Rukenshia/terminal.scale/docs/schematics.kicad_sch

## KiCad design docs/schematics.kicad_sch (2025-04-18)

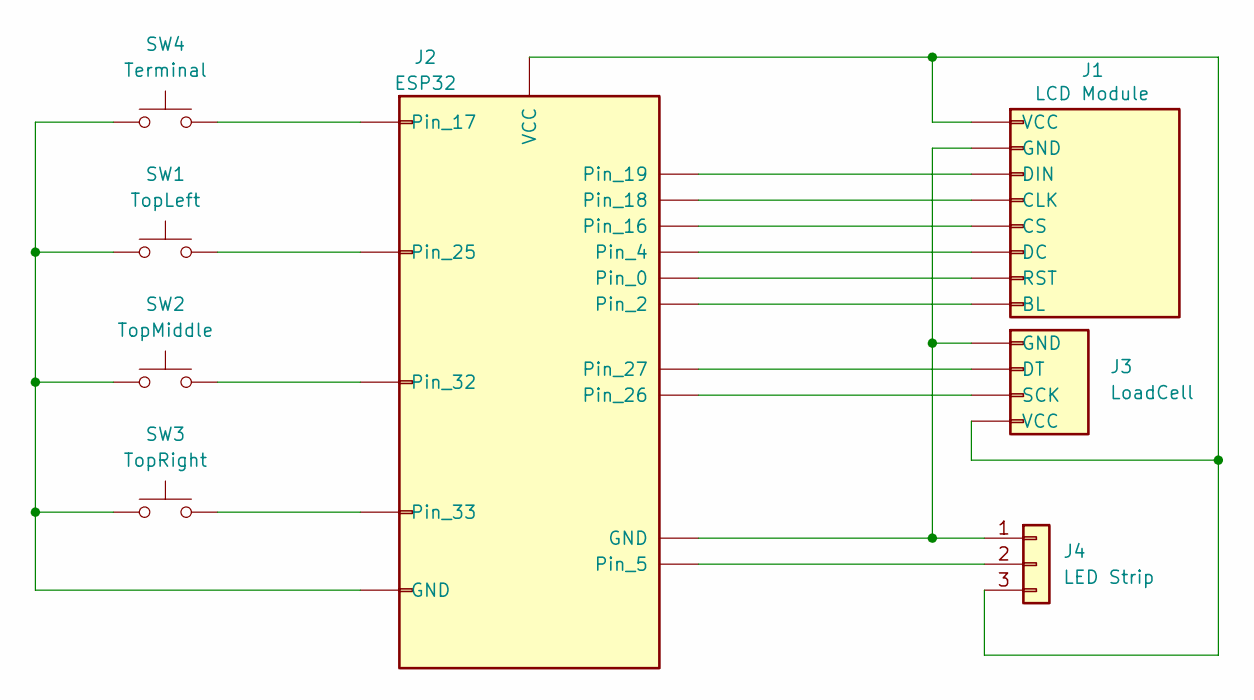
[picture p18: schematic schematics.kicad_sch]

Parts:
J1: LCD Module
J2: ESP32
J3: LoadCell
J4: LED Strip
SW1: TopLeft
SW2: TopMiddle
SW3: TopRight
SW4: Terminal

Connections:
unnamed: J1.1 (VCC), J2.2 (VCC), J3.4 (VCC), J4.3
unnamed: J1.2 (GND), J2.GND, J3.1 (GND), J4.1
unnamed: J1.3 (DIN), J2.19
unnamed: J1.4 (CLK), J2.18
unnamed: J1.5 (CS), J2.16
unnamed: J1.6 (DC), J2.4
unnamed: J1.7 (RST), J2.0
unnamed: J1.8 (BL), J2.2 (VCC)
unnamed: J2.5, J4.2
unnamed: J2.17, SW4.2
unnamed: J2.25, SW1.2
unnamed: J2.26, J3.3 (SCK)
unnamed: J2.27, J3.2 (DT)
unnamed: J2.32, SW2.2
unnamed: J2.33, SW3.2
unnamed: J2.GND, SW1.1, SW2.1, SW3.1, SW4.1
