Rukenshia/terminal.scale/src/store.cpp

#include "store.h"
#include "debug.h"
#include "buttons.h"

void Store::exit()
{
    reset();
    ledStrip.turnOff();
}

void Store::draw()
{
    if (!tainted)
    {
        return;
    }
    tainted = false;

    if (ui.menu->current == STORE_ORDERS)
    {
        drawOrders();
        return;
    }
    else if (ui.menu->current == STORE_BROWSE)
    {
        drawProducts();
        return;
    }

    // clear the screen except menu clearance
    tft.fillRect(0, Menu::menuClearance, tft.width(), tft.height() - Menu::menuClearance, BACKGROUND_COLOR);

    auto bounds = ui.typeText("Store", titleText);
    delay(1000);
    ui.wipeText(bounds);

    tft.setFreeFont(&GeistMono_VariableFont_wght18pt7b);
    tft.setTextColor(ACCENT_COLOR);
}

void Store::loadOrders()
{
    if (ordersLoaded)
    {
        Serial.println("Orders already loaded");
        return;
    }

    tft.fillScreen(BACKGROUND_COLOR);
    auto bounds = ui.typeTitle("Loading orders");
    ui.startBlinking();

#ifdef NO_WIFI
    orders = {
        {"id1", "2025-01-01T12:34:56Z", 1, {"John Doe", "123 Main St", "", "New York", "NY", "10001", "USA", "555-1234"}, {1000, 50}, {"UPS", "1234567890", "SHIPPED", "http://example.com/track"}},
        {"id2", "2024-12-20T34:56:00Z", 2, {"Jane Smith", "456 Elm St", "", "Los Angeles", "CA", "90001", "USA", "555-5678"}, {2000, 100}, {"FedEx", "0987654321", "DELIVERED", "http://example.com/track"}},
    };
#else
    orders = terminalApi.getOrders();
    Serial.printf("Loaded %d orders\n", orders.size());
#endif
    ordersLoaded = true;

    ui.stopBlinking();
    ui.wipeText(bounds);

    if (orders.empty())
    {
        ui.typeTitle("No orders found");
        delay(2000);

        ui.menu->selectMenu(STORE);
        return;
    }

    recalcMenuButtons(orderIndex, orders.size());
    ui.menu->taint();
}

void Store::drawOrders()
{
    if (!ordersLoaded)
    {
        loadOrders();

        if (orders.empty())
        {
            return;
        }
        recalcMenuButtons(orderIndex, orders.size());
    }

    tft.fillRect(0, Menu::menuClearance - tft.fontHeight(), tft.width(), tft.height(), BACKGROUND_COLOR);

    const uint16_t startY = Menu::menuClearance + 40;

    tft.setTextColor(ACCENT_COLOR);
    tft.setCursor(20, startY);

    auto &order = orders[orderIndex];
    String orderId = order.id.substring(0, 16) + "..";
    ui.setIdealFont(orderId.c_str(), 30);

    tft.print(orderId);

    String status = "UNKNOWN";
    if (!order.tracking.status.isEmpty())
    {
        status = order.tracking.status;
    }

    tft.setCursor(20, startY + 40);

    String subheaderText = order.created.substring(0, 10) + " - " + status;
    ui.setIdealFont(subheaderText.c_str(), 30);
    tft.setTextColor(TEXT_COLOR);
    tft.print(order.created.substring(0, 10).c_str());
    tft.print(" - ");

    if (status == "DELIVERED")
    {
        tft.setTextColor(0x05C8);
    }
    else if (status == "UNKNOWN")
    {
        tft.setTextColor(0xD9A7);
    }
    else
    {
        tft.setTextColor(0x44FC);
    }

    tft.print(status.c_str());

    ui.drawProgressIndicator(orderIndex, orders.size());
}

void Store::recalcMenuButtons(int index, int size)
{
    bool shouldRedraw = false;

    if (index == size - 1)
    {
        ui.menu->hideButton(MenuButton::RIGHT);
        shouldRedraw = true;
    }
    else if (!ui.menu->isButtonVisible(MenuButton::RIGHT))
    {
        ui.menu->showButton(MenuButton::RIGHT);
        shouldRedraw = true;
    }

    if (index == 0)
    {
        ui.menu->hideButton(MenuButton::LEFT);
        shouldRedraw = true;
    }
    else if (!ui.menu->isButtonVisible(MenuButton::LEFT))
    {
        ui.menu->showButton(MenuButton::LEFT);
        shouldRedraw = true;
    }

    if (shouldRedraw)
    {
        ui.menu->redraw();
    }

    ledStrip.scrollIndicator(index, size);
}

void Store::nextOrder()
{
    orderIndex++;
    if (orderIndex >= orders.size())
    {
        orderIndex--;
        return;
    }

    recalcMenuButtons(orderIndex, orders.size());
    taint();
}

void Store::previousOrder()
{
    if (orderIndex == 0)
    {
        return;
    }

    orderIndex--;
    recalcMenuButtons(orderIndex, orders.size());
    taint();
}

void Store::drawProducts()
{
    if (!productsLoaded)
    {
        loadProducts();

        if (products.empty())
        {
            return;
        }
        recalcMenuButtons(productIndex, products.size());
    }

    uint16_t y = 60 + 60;
    tft.fillRect(0, Menu::menuClearance - tft.fontHeight(), tft.width(), tft.height(), BACKGROUND_COLOR);

    tft.setFreeFont(&GeistMono_VariableFont_wght14pt7b);
    tft.setTextColor(ACCENT_COLOR);
    tft.setCursor(tft.width() - 20 - tft.textWidth("B") / 2, y);
    tft.print("B");
    tft.setCursor(tft.width() - 20 - tft.textWidth("U") / 2, y + tft.fontHeight() + 4);
    tft.print("U");
    tft.setCursor(tft.width() - 20 - tft.textWidth("Y") / 2, y + tft.fontHeight() * 2 + 8);
    tft.print("Y");

    y += 20;

    tft.setFreeFont(&GeistMono_VariableFont_wght18pt7b);

    tft.setTextColor(ACCENT_COLOR);
    tft.setCursor(20, y);

    auto &product = products[productIndex];
    ui.setIdealFont(product.name.c_str());
    tft.print(product.name.c_str());

    y += 40;
    tft.setCursor(20, y);

    String subheader = product.variants[0].name + " - $" + String(product.variants[0].price / 100.0f, 2);
    ui.setIdealFont(subheader.c_str(), nonTitleFonts);
    tft.setTextColor(TEXT_COLOR);
    tft.print(subheader.c_str());

    ui.drawProgressIndicator(productIndex, products.size());
}

void Store::loadProducts()
{
    tft.fillScreen(BACKGROUND_COLOR);
    auto bounds = ui.typeTitle("Loading products");
    ui.startBlinking();

#ifdef NO_WIFI
    products = std::vector<Product>{
        Product{"id1", "flow", "coffee", {Variant{"id1", "12oz", 1000}}},
        Product{"id2", "[object Object]", "covfefe", {Variant{"id2", "24oz", 2000}}},
    };
#else
    products = terminalApi.getProducts();
#endif

    // FIXME: would be nice to support more than 12oz bags
    // @terminal.shop when in europe?
    for (auto &product : products)
    {
        product.variants.erase(
            std::remove_if(product.variants.begin(), product.variants.end(),
                           [](const Variant &variant)
                           { return variant.name != "12oz"; }),
            product.variants.end());
    }

    productsLoaded = true;

    ui.stopBlinking();
    ui.wipeText(bounds);

    if (products.empty())
    {
        ui.typeTitle("No products found");
        delay(2000);

        ui.menu->selectMenu(STORE);
        return;
    }

    ui.menu->taint();
}

void Store::previousProduct()
{
    if (productIndex == 0)
    {
        return;
    }

    productIndex--;

    recalcMenuButtons(productIndex, products.size());
    taint();
}

void Store::nextProduct()
{
    if (productIndex >= products.size() - 1)
    {
        return;
    }

    productIndex++;

    recalcMenuButtons(productIndex, products.size());
    taint();
}

void Store::buyProduct()
{
    tft.setFreeFont(&GeistMono_VariableFont_wght18pt7b);
    tft.fillScreen(BACKGROUND_COLOR);
    tft.setTextColor(TEXT_COLOR);

    auto tw = tft.textWidth("Hold to buy");
    tft.setCursor(tft.width() / 2 - tw / 2, tft.height() / 2);
    tft.print("Hold to buy");

    const uint16_t initialCircleSize = 20;
    const uint16_t animationDuration = 3000; // 3 seconds total
    const uint16_t maxCircleSize = tft.width() * 2 + initialCircleSize / 2;
    const uint16_t circleX = tft.width() + initialCircleSize / 2;
    const uint16_t circleY = tft.height() / 2 + 40;

    tft.fillCircle(circleX, circleY, initialCircleSize, ACCENT_COLOR);
    delay(1000);

    bool finished = false;
    unsigned long startTime = millis();
    unsigned long elapsedTime = 0;

    uint16_t circleSize = initialCircleSize;

    while (digitalRead(PIN_TERMINAL_BUTTON) == LOW)
    {
        elapsedTime = millis() - startTime;

        float linearProgress = min(1.0f, (float)elapsedTime / animationDuration);
        // Easing function: accelerate towards the end (ease-in-quad)
        float easedProgress = linearProgress * linearProgress;
        circleSize = (easedProgress * maxCircleSize) + initialCircleSize;

        tft.fillCircle(circleX, circleY, circleSize, ACCENT_COLOR);

        auto color = RgbColor::LinearBlend(
            RgbColor(194, 126, 0),
            RgbColor(255, 94, 0), linearProgress);
        ledStrip.reverseProgress(linearProgress, color);

        if (elapsedTime >= animationDuration)
        {
            finished = true;
            break;
        }
        delay(10);
    }

    if (!finished)
    {
        ui.menu->taint();
        taint();
        recalcMenuButtons(productIndex, products.size());
        return;
    }

    orderProduct(products[productIndex],
                 products[productIndex].variants[0]);
}

void Store::orderProduct(String bagName)
{
    if (!productsLoaded)
    {
        loadProducts();
        if (products.empty())
        {
            return;
        }
    }

    auto index = std::find_if(products.begin(), products.end(),
                              [&bagName](const Product &product)
                              {
                                  return product.name == bagName;
                              }) -
                 products.begin();

    orderProduct(products[index], products[index].variants[0]);
}

void Store::orderProduct(Product product, Variant variant)
{
    tft.fillScreen(BACKGROUND_COLOR);
    auto bounds = ui.typeTitle("Clearing cart...");
    if (terminalApi.clearCart())
    {
        Serial.println("Cart cleared");
    }
    else
    {
        Serial.println("Failed to clear cart");
    }

    ui.wipeText(bounds);
    bounds = ui.typeTitle("Adding to cart...");
    Cart *cart = terminalApi.addItemToCart(products[productIndex].variants[0].id.c_str(), 1);
    if (!cart)
    {
        taint();
        ui.menu->taint();
        return;
    }
    ui.wipeText(bounds);

    bounds = ui.typeTitle(String("Subtotal: $" + String((float)cart->subtotal / 100, 2)).c_str());
    delay(3000);
    ui.wipeText(bounds);

    bounds = ui.typeTitle("Placing order...");
    Order *order = terminalApi.convertCartToOrder();
    if (!order)
    {
        taint();
        ui.menu->taint();
        return;
    }

    ui.wipeText(bounds);
    ui.typeTitle("Order placed");
    ledStrip.purchaseAnimation();
    delay(5000);
    ui.wipeText(bounds);

    ledStrip.turnOff();
    taint();
    ui.menu->selectMenu(MAIN_MENU);
}

void Store::openToReorder(String bagName)
{
    tft.fillScreen(BACKGROUND_COLOR);

    loadProducts();
    if (products.empty())
    {
        Serial.println("No products found");
        return;
    }

    ui.menu->selectMenu(STORE_BROWSE);

    // set index
    productIndex = std::find_if(products.begin(), products.end(),
                                [&bagName](const Product &product)
                                {
                                    return product.name == bagName;
                                }) -
                   products.begin();
    Serial.printf("Product index: %d\n", productIndex);
    if (productIndex >= products.size())
    {
        productIndex = 0;
    }

    Serial.printf("Product name: %s\n", products[productIndex].name.c_str());
    recalcMenuButtons(productIndex, products.size());
    taint();
}
