Rukenshia/terminal.scale/include/HelvetiPixelFont_wght12.h

const uint8_t HelvetiPixel12pt7bBitmaps[] PROGMEM = {
  0x00, 0xFF, 0xFF, 0xCF, 0xDE, 0xF7, 0xBD, 0x80, 0x1B, 0x0D, 0x86, 0xDF,
  0xFF, 0xFB, 0x61, 0xB1, 0xFF, 0xFF, 0xB6, 0x1B, 0x0D, 0x80, 0x18, 0x18,
  0x7C, 0xFF, 0xDB, 0xD8, 0xFC, 0x7C, 0x1B, 0xDB, 0xDB, 0x7C, 0x7C, 0x18,
  0x30, 0xC7, 0xC6, 0x36, 0x31, 0xB6, 0x0F, 0xB0, 0x19, 0x80, 0x19, 0x80,
  0xDF, 0x06, 0xD8, 0xC6, 0xC6, 0x3E, 0x30, 0xC0, 0x1C, 0x0F, 0xE1, 0x8C,
  0x31, 0x87, 0xF0, 0x38, 0x1B, 0x1F, 0x7F, 0xC3, 0x98, 0x73, 0xFF, 0xBE,
  0x30, 0xFF, 0xC0, 0x1B, 0xD8, 0xCE, 0x63, 0x18, 0xC6, 0x38, 0xC6, 0x3C,
  0x60, 0xC7, 0x18, 0xC7, 0x8C, 0x63, 0x18, 0xDE, 0xC6, 0x73, 0x00, 0xDB,
  0xDB, 0x7C, 0xFF, 0xDB, 0x18, 0x18, 0x18, 0xFF, 0xFF, 0x18, 0x18, 0x18,
  0x6D, 0xFC, 0xFF, 0xC0, 0xF0, 0x18, 0xC6, 0x37, 0xB1, 0x8C, 0x66, 0x31,
  0x8C, 0x60, 0x7C, 0xFF, 0xC3, 0xC3, 0xC3, 0xC3, 0xC3, 0xC3, 0xC3, 0xC3,
  0xFF, 0x7C, 0x19, 0xCF, 0xBD, 0x8C, 0x63, 0x18, 0xC6, 0x30, 0x7C, 0xFF,
  0xC3, 0x03, 0x0F, 0x0C, 0x18, 0x78, 0x60, 0xC0, 0xFF, 0xFF, 0x7C, 0xFF,
  0xC3, 0x03, 0x1F, 0x1C, 0x03, 0x03, 0x03, 0xC3, 0xFF, 0x7C, 0x03, 0x07,
  0x83, 0xC3, 0x67, 0xB3, 0x1B, 0x0D, 0xFF, 0xFF, 0x81, 0x80, 0xC0, 0x60,
  0xFF, 0xFF, 0xC0, 0xC0, 0xFC, 0xFC, 0x03, 0x03, 0x03, 0xC3, 0xFF, 0x7C,
  0x7C, 0xFF, 0xC3, 0xC0, 0xFC, 0xFC, 0xC3, 0xC3, 0xC3, 0xC3, 0xFF, 0x7C,
  0xFF, 0xFF, 0x03, 0x0C, 0x0C, 0x0C, 0x18, 0x18, 0x18, 0x60, 0x60, 0x60,
  0x7C, 0xFF, 0xC3, 0xC3, 0xFF, 0x7C, 0xC3, 0xC3, 0xC3, 0xC3, 0xFF, 0x7C,
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
  {   377,   8,  12,  11,    1,  -11 },   // 0x46 'F'
  {   389,  11,  12,  12,    0,  -11 },   // 0x47 'G'
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

const GFXfont HelvetiPixel12pt7b PROGMEM = {
  (uint8_t  *)HelvetiPixel12pt7bBitmaps,
  (GFXglyph *)HelvetiPixel12pt7bGlyphs,
  0x20, 0x7E, 22 };

// Approx. 1628 bytes
