Rukenshia/terminal.scale/include/GeistMonoVariableFont_wght10.h

const uint8_t GeistMono_VariableFont_wght10pt7bBitmaps[] PROGMEM = {
  0x00, 0xFF, 0xFF, 0xE0, 0xF0, 0xCE, 0x72, 0x94, 0xA5, 0x20, 0x19, 0x86,
  0x61, 0x90, 0x44, 0x7F, 0xC4, 0xC3, 0x30, 0xC8, 0x22, 0x3F, 0xE2, 0x61,
  0x98, 0x64, 0x11, 0x00, 0x0C, 0x03, 0x01, 0xE1, 0xFC, 0xCD, 0xB3, 0x2C,
  0xCD, 0xB0, 0x7C, 0x07, 0xC0, 0xD9, 0x33, 0xCC, 0xF3, 0x37, 0xD8, 0xFC,
  0x0C, 0x03, 0x00, 0x78, 0x64, 0x8C, 0xCC, 0x8C, 0xD8, 0xCD, 0x04, 0xB0,
  0x36, 0x00, 0x4C, 0x0F, 0xE0, 0xA2, 0x1A, 0x33, 0x22, 0x23, 0x26, 0x1C,
  0x1E, 0x07, 0x60, 0xC4, 0x18, 0x83, 0x30, 0x3C, 0x07, 0x01, 0xE0, 0x66,
  0x68, 0x6F, 0x0D, 0xE0, 0xE6, 0x1C, 0x7E, 0xC0, 0xFF, 0xF8, 0x32, 0x64,
  0xCC, 0xCC, 0x8C, 0xCC, 0xC4, 0x62, 0x30, 0x8C, 0x66, 0x23, 0x33, 0x33,
  0x33, 0x26, 0x64, 0xC0, 0x49, 0xE3, 0x3F, 0x71, 0x24, 0x80, 0x0C, 0x03,
  0x00, 0xC3, 0xFF, 0xFF, 0xC3, 0x00, 0xC0, 0x30, 0x0C, 0x00, 0xF6, 0x80,
  0xFC, 0xF0, 0x03, 0x02, 0x06, 0x06, 0x04, 0x0C, 0x08, 0x08, 0x18, 0x10,
  0x30, 0x30, 0x20, 0x60, 0x60, 0x40, 0xC0, 0x3E, 0x1D, 0xC6, 0x1B, 0x0E,
  0xC6, 0xF1, 0xBC, 0xCF, 0x23, 0xD8, 0xF4, 0x3F, 0x19, 0x86, 0x73, 0x0F,
  0x80, 0x04, 0x01, 0x07, 0xC1, 0xF0, 0x04, 0x01, 0x00, 0x40, 0x10, 0x04,
  0x01, 0x00, 0x40, 0x10, 0xFF, 0xFF, 0xF0, 0x3F, 0x1C, 0xE6, 0x0F, 0x03,
  0x00, 0xC0, 0x60, 0x38, 0x3C, 0x1C, 0x0C, 0x06, 0x03, 0x00, 0xFF, 0xFF,
  0xF0, 0x3F, 0x1C, 0xEC, 0x18, 0x02, 0x01, 0x80, 0xE0, 0xE0, 0x0E, 0x00,
  0x80, 0x3C, 0x0F, 0x03, 0x63, 0x8F, 0xC0, 0x03, 0x01, 0xC0, 0x70, 0x34,
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
  {   504,  10,  14,  12,    1,  -13 },   // 0x47 'G'
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

const GFXfont GeistMono_VariableFont_wght10pt7b PROGMEM = {
  (uint8_t  *)GeistMono_VariableFont_wght10pt7bBitmaps,
  (GFXglyph *)GeistMono_VariableFont_wght10pt7bGlyphs,
  0x20, 0x7E, 25 };

// Approx. 1972 bytes
