Rukenshia/terminal.scale/include/GeistMonoVariableFont_wght14.h

const uint8_t GeistMono_VariableFont_wght14pt7bBitmaps[] PROGMEM = {
  0x00, 0xDB, 0x6D, 0xB6, 0xDB, 0x6C, 0x00, 0xFF, 0x80, 0xCF, 0x9F, 0x3E,
  0x7C, 0xF9, 0xB3, 0x66, 0xCC, 0x06, 0x18, 0x18, 0xC0, 0x63, 0x01, 0x8C,
  0x0C, 0x30, 0xFF, 0xF7, 0xFF, 0xC3, 0x18, 0x0C, 0x60, 0x71, 0x81, 0x86,
  0x06, 0x18, 0x7F, 0xFB, 0xFF, 0xE1, 0x8C, 0x0C, 0x30, 0x30, 0xC0, 0xC6,
  0x03, 0x18, 0x00, 0x03, 0x00, 0x0C, 0x00, 0x30, 0x07, 0xF8, 0x3F, 0xF1,
  0xCC, 0xE6, 0x31, 0x98, 0xC7, 0x63, 0x1D, 0xCC, 0x07, 0xB0, 0x0F, 0xC0,
  0x0F, 0xE0, 0x0F, 0xE0, 0x33, 0xC0, 0xC7, 0xE3, 0x0D, 0x8C, 0x37, 0x31,
  0xDE, 0xCF, 0x3F, 0xF8, 0x3F, 0xC0, 0x30, 0x00, 0xC0, 0x18, 0x00, 0x7E,
  0x0E, 0x67, 0x0C, 0xC3, 0x18, 0xC3, 0x18, 0xC3, 0x30, 0xC3, 0x70, 0x63,
  0x60, 0x7E, 0xC0, 0x3C, 0xC0, 0x01, 0x80, 0x03, 0xBE, 0x03, 0x67, 0x06,
  0x63, 0x06, 0xC3, 0x0C, 0xC3, 0x1C, 0xC3, 0x18, 0x63, 0x30, 0x7E, 0x70,
  0x3C, 0x0F, 0x00, 0x7F, 0x80, 0xE7, 0x01, 0x87, 0x07, 0x0E, 0x0E, 0x1C,
  0x0C, 0x70, 0x1D, 0xC0, 0x1F, 0x00, 0x3C, 0x00, 0xF8, 0x03, 0xB8, 0x6E,
  0x38, 0xD8, 0x39, 0xB0, 0x33, 0x60, 0x7E, 0xC0, 0x79, 0xC0, 0xF1, 0xFF,
  0xF1, 0xFE, 0x70, 0xFF, 0xFF, 0xC0, 0x0C, 0x71, 0x8E, 0x30, 0xC6, 0x18,
  0x63, 0x8E, 0x38, 0xE3, 0x8E, 0x18, 0x61, 0x87, 0x0C, 0x30, 0x61, 0x83,
  0xC1, 0x87, 0x0C, 0x38, 0x61, 0x87, 0x1C, 0x30, 0xC3, 0x0C, 0x30, 0xC7,
  0x1C, 0x61, 0x8E, 0x30, 0xC6, 0x38, 0x22, 0x33, 0x0D, 0x87, 0x8F, 0xFF,
  0xFC, 0xF0, 0x6C, 0x66, 0x11, 0x00, 0x06, 0x00, 0x30, 0x01, 0x80, 0x0C,
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
  {   954,  14,  20,  16,    1,  -19 },   // 0x47 'G'
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

const GFXfont GeistMono_VariableFont_wght14pt7b PROGMEM = {
  (uint8_t  *)GeistMono_VariableFont_wght14pt7bBitmaps,
  (GFXglyph *)GeistMono_VariableFont_wght14pt7bGlyphs,
  0x20, 0x7E, 36 };

// Approx. 3171 bytes
