Rukenshia/terminal.scale/include/GeistMonoVariableFont_wght12.h

const uint8_t GeistMono_VariableFont_wght12pt7bBitmaps[] PROGMEM = {
  0x00, 0xDB, 0x6D, 0xB6, 0xDB, 0x60, 0x3F, 0xE0, 0xCF, 0x3C, 0xF3, 0xCF,
  0x3C, 0xD3, 0x0C, 0x60, 0xC6, 0x0C, 0x40, 0xCC, 0x08, 0xC7, 0xFF, 0x7F,
  0xF1, 0x88, 0x18, 0x81, 0x18, 0x11, 0x8F, 0xFE, 0x31, 0x83, 0x10, 0x33,
  0x02, 0x30, 0x63, 0x00, 0x06, 0x00, 0x60, 0x0F, 0x03, 0xFC, 0x77, 0xE6,
  0x66, 0xE6, 0x7E, 0x63, 0x66, 0x07, 0xE0, 0x1F, 0x80, 0x7E, 0x06, 0xE0,
  0x63, 0xC6, 0x3E, 0x63, 0x76, 0x73, 0xFE, 0x1F, 0xC0, 0x60, 0x06, 0x00,
  0x38, 0x19, 0xF0, 0xCC, 0x63, 0x31, 0x98, 0xC6, 0x43, 0x1B, 0x06, 0x78,
  0x1F, 0x60, 0x03, 0x00, 0x09, 0xC0, 0x6D, 0x83, 0x63, 0x0D, 0x8C, 0x66,
  0x31, 0x18, 0xCC, 0x36, 0x60, 0xF0, 0x0F, 0x80, 0x7F, 0x03, 0x8C, 0x0C,
  0x30, 0x30, 0xC0, 0xE7, 0x01, 0xB8, 0x03, 0xC0, 0x1E, 0x00, 0xFC, 0x06,
  0x31, 0x98, 0x66, 0xE1, 0xDB, 0x83, 0xC6, 0x07, 0x1F, 0xFC, 0x3F, 0xDC,
  0xFF, 0xFF, 0x19, 0x88, 0xC6, 0x63, 0x18, 0xC6, 0x31, 0x8C, 0x63, 0x18,
  0x63, 0x08, 0x61, 0x80, 0x86, 0x18, 0xC6, 0x18, 0xC6, 0x31, 0xC6, 0x73,
  0x18, 0xC6, 0x63, 0x19, 0x88, 0x00, 0x24, 0x66, 0x3C, 0xFF, 0xFF, 0x3C,
  0x24, 0x66, 0x06, 0x00, 0x60, 0x06, 0x00, 0x60, 0x06, 0x0F, 0xFF, 0xFF,
  0xF0, 0x60, 0x06, 0x00, 0x60, 0x06, 0x00, 0x60, 0xFD, 0xE8, 0xFF, 0xFF,
  0xFF, 0x80, 0x01, 0x81, 0x80, 0xC0, 0x40, 0x60, 0x30, 0x10, 0x18, 0x0C,
  0x0C, 0x06, 0x03, 0x03, 0x01, 0x80, 0xC0, 0xC0, 0x60, 0x30, 0x30, 0x18,
  0x08, 0x00, 0x0F, 0x03, 0xFC, 0x30, 0xE6, 0x0E, 0x61, 0xEE, 0x1F, 0xC3,
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
  {   732,  12,  17,  14,    1,  -16 },   // 0x47 'G'
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

const GFXfont GeistMono_VariableFont_wght12pt7b PROGMEM = {
  (uint8_t  *)GeistMono_VariableFont_wght12pt7bBitmaps,
  (GFXglyph *)GeistMono_VariableFont_wght12pt7bGlyphs,
  0x20, 0x7E, 31 };

// Approx. 2568 bytes
