Rukenshia/terminal.scale/include/GeistMonoVariableFont_wght16.h

const uint8_t GeistMono_VariableFont_wght16pt7bBitmaps[] PROGMEM = {
  0x00, 0x77, 0x77, 0x77, 0x77, 0x77, 0x77, 0x66, 0x60, 0x00, 0xFF, 0xFF,
  0xE3, 0xE3, 0xE3, 0xE3, 0x63, 0x63, 0x63, 0x63, 0x63, 0x63, 0x07, 0x1C,
  0x0C, 0x30, 0x18, 0x60, 0x30, 0xC0, 0xE1, 0x81, 0x87, 0x1F, 0xFF, 0xBF,
  0xFF, 0x0C, 0x30, 0x38, 0x60, 0x71, 0xC0, 0xC3, 0x81, 0x86, 0x03, 0x0C,
  0x3F, 0xFF, 0x7F, 0xFE, 0x30, 0xE0, 0x61, 0x80, 0xC3, 0x01, 0x86, 0x07,
  0x0C, 0x0C, 0x38, 0x00, 0x01, 0xC0, 0x01, 0xC0, 0x01, 0xC0, 0x0F, 0xF0,
  0x1F, 0xF8, 0x3F, 0xFC, 0x79, 0xCE, 0x71, 0xCF, 0x71, 0xC7, 0x71, 0xC7,
  0x71, 0xC0, 0x79, 0xC0, 0x3F, 0xC0, 0x1F, 0xE0, 0x03, 0xFC, 0x01, 0xFE,
  0x01, 0xCF, 0x01, 0xC7, 0xE1, 0xC7, 0x71, 0xC3, 0x71, 0xC7, 0x79, 0xC7,
  0x3F, 0xDF, 0x1F, 0xFE, 0x07, 0xF8, 0x01, 0xC0, 0x01, 0xC0, 0x01, 0xC0,
  0x08, 0x00, 0x0F, 0xC0, 0xE7, 0xF0, 0x31, 0x86, 0x1C, 0xE1, 0x86, 0x38,
  0x63, 0x0E, 0x19, 0xC3, 0x86, 0x60, 0x61, 0xB8, 0x1D, 0xCC, 0x03, 0xF6,
  0x00, 0x33, 0x80, 0x00, 0xCF, 0x00, 0x77, 0xE0, 0x1B, 0x9C, 0x0C, 0xC3,
  0x07, 0x30, 0xC1, 0x9C, 0x30, 0xE7, 0x0C, 0x30, 0xC3, 0x18, 0x31, 0xCE,
  0x0F, 0xE3, 0x01, 0xF0, 0x07, 0x80, 0x0F, 0xF0, 0x0F, 0xFC, 0x07, 0x0E,
  0x03, 0x87, 0x01, 0xC1, 0x80, 0xE1, 0xC0, 0x70, 0xE0, 0x1C, 0xE0, 0x0F,
  0xE0, 0x03, 0xE0, 0x03, 0xE0, 0x03, 0xF8, 0x03, 0xDC, 0x1F, 0xC7, 0x0F,
  0xC1, 0xC6, 0xE0, 0x77, 0x60, 0x3F, 0xB8, 0x0F, 0x9C, 0x03, 0xCF, 0x03,
  0xE3, 0xFF, 0xF8, 0xFF, 0xCE, 0x04, 0x00, 0xFF, 0xFF, 0xFE, 0xD8, 0x0E,
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
  {  1261,  16,  24,  19,    1,  -22 },   // 0x47 'G'
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

const GFXfont GeistMono_VariableFont_wght16pt7b PROGMEM = {
  (uint8_t  *)GeistMono_VariableFont_wght16pt7bBitmaps,
  (GFXglyph *)GeistMono_VariableFont_wght16pt7bGlyphs,
  0x20, 0x7E, 41 };

// Approx. 3967 bytes
