Rukenshia/terminal.scale/include/GeistMonoVariableFont_wght18.h

const uint8_t GeistMono_VariableFont_wght18pt7bBitmaps[] PROGMEM = {
  0x00, 0x73, 0x9C, 0xE7, 0x39, 0xCE, 0x73, 0x9C, 0xE7, 0x39, 0xCE, 0x31,
  0x80, 0x00, 0x7F, 0xFF, 0xF8, 0xE3, 0xF1, 0xF8, 0xFC, 0x7E, 0x3F, 0x1F,
  0x8F, 0xC7, 0x63, 0xB1, 0xD8, 0xCC, 0x60, 0x03, 0x87, 0x01, 0x83, 0x00,
  0xC1, 0x80, 0x61, 0xC0, 0x70, 0xE0, 0x38, 0x70, 0x1C, 0x30, 0xFF, 0xFF,
  0x7F, 0xFF, 0x87, 0x0E, 0x03, 0x87, 0x01, 0xC3, 0x80, 0xC1, 0x80, 0x60,
  0xC0, 0x70, 0xE0, 0x38, 0x70, 0xFF, 0xFF, 0x7F, 0xFF, 0x86, 0x0C, 0x03,
  0x0E, 0x03, 0x87, 0x01, 0xC3, 0x80, 0xE1, 0x80, 0x60, 0xC0, 0x30, 0xE0,
  0x00, 0x01, 0xC0, 0x00, 0x70, 0x00, 0x1C, 0x00, 0x1F, 0xC0, 0x1F, 0xFC,
  0x0F, 0xFF, 0x87, 0x9D, 0xF1, 0xC7, 0x3C, 0xF1, 0xC7, 0xB8, 0x70, 0xEE,
  0x1C, 0x3B, 0xC7, 0x00, 0x79, 0xC0, 0x1F, 0xF0, 0x03, 0xFC, 0x00, 0x3F,
  0xE0, 0x03, 0xFE, 0x00, 0x7F, 0xC0, 0x1C, 0xF8, 0x07, 0x0E, 0xE1, 0xC3,
  0xB8, 0x70, 0xFF, 0x1C, 0x3F, 0xC7, 0x0E, 0x79, 0xC7, 0x8F, 0xF7, 0xC1,
  0xFF, 0xE0, 0x3F, 0xF0, 0x01, 0xC0, 0x00, 0x70, 0x00, 0x1C, 0x00, 0x1F,
  0x00, 0xE1, 0xFC, 0x07, 0x1C, 0x70, 0x70, 0xC1, 0x83, 0x0E, 0x0C, 0x38,
  0x70, 0x73, 0x83, 0x83, 0x1C, 0x1C, 0x19, 0xC0, 0x61, 0xCC, 0x03, 0x8E,
  0xE0, 0x0F, 0xEE, 0x00, 0x3E, 0x70, 0x00, 0x07, 0x00, 0x00, 0x33, 0xE0,
  0x03, 0xBF, 0x80, 0x3B, 0x8E, 0x01, 0xDC, 0x30, 0x1C, 0xC1, 0xC0, 0xC6,
  0x0E, 0x0E, 0x30, 0x70, 0xE1, 0x83, 0x87, 0x0E, 0x18, 0x70, 0x71, 0xC3,
  0x01, 0xFC, 0x38, 0x07, 0xC0, 0x01, 0xC0, 0x01, 0xFE, 0x00, 0x7F, 0xE0,
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
  {  1607,  19,  27,  21,    1,  -25 },   // 0x47 'G'
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

const GFXfont GeistMono_VariableFont_wght18pt7b PROGMEM = {
  (uint8_t  *)GeistMono_VariableFont_wght18pt7bBitmaps,
  (GFXglyph *)GeistMono_VariableFont_wght18pt7bGlyphs,
  0x20, 0x7E, 46 };

// Approx. 4849 bytes
