Rukenshia/terminal.scale/include/led.h

#ifndef LED_H
#define LED_H

#include <Arduino.h>
#include <NeoPixelBusLg.h>
#include <NeoPixelAnimator.h>

#define NUM_LEDS 8
#define LED_DATA_PIN 5

struct AnimationData;

class LedStrip
{
private:
    NeoPixelBusLg<NeoGrbFeature, NeoWs2812Method> strip;

    TaskHandle_t animationTaskHandle = NULL;
    NeoPixelAnimator animator = NeoPixelAnimator(1);

    void createAnimationTask(AnimationData *data);

public:
    LedStrip();
    void begin();

    void turnOff();

    void progress(float percentage, RgbColor color = RgbColor(255, 94, 0));
    void reverseProgress(float percentage, RgbColor color = RgbColor(255, 94, 0));
    void scrollIndicator(uint index, uint size, RgbColor color = RgbColor(255, 94, 0));

    void setColor(RgbColor color)
    {
        for (int i = 0; i < NUM_LEDS; i++)
        {
            strip.SetPixelColor(i, color);
        }
        strip.Show();
    }

    void turnOnAnimation();
    void turnOffAnimation();

    void purchaseAnimation();

    void reorderAnimation();
    void reorderIndication();
    bool showingReorderIndicator = false;

    static void animationTask(void *parameter);
};

struct AnimationData
{
    LedStrip *instance;
    RgbColor start;
    RgbColor end;
    AnimEaseFunction easeFunction;
    uint32_t duration;
    bool reverse = false;
    bool loop = false;
};

#endif
