Rukenshia/terminal.scale/include/store.h

#ifndef STORE_H
#define STORE_H

#include <Arduino.h>
#include "ui.h"
#include "scale.h"
#include "terminal_api.h"

class Store
{
private:
    UI &ui;
    TFT_eSPI &tft;
    Scale &scaleManager;
    TerminalApi &terminalApi;
    LedStrip &ledStrip;

    bool tainted = false;

    std::vector<Order> orders;
    bool ordersLoaded = false;
    uint orderIndex = 0;
    void drawOrders();
    void loadOrders();

    std::vector<Product> products;
    bool productsLoaded = false;
    uint productIndex = 0;
    void drawProducts();
    void loadProducts();

    void recalcMenuButtons(int index, int size);

public:
    Store(UI &uiInstance, TFT_eSPI &tftDisplay, Scale &scaleInstance, TerminalApi &terminalApi, LedStrip &ledStrip)
        : ui(uiInstance), tft(tftDisplay), scaleManager(scaleInstance), terminalApi(terminalApi), ledStrip(ledStrip) {}

    void exit();
    void taint() { tainted = true; };
    void draw();

    void openToReorder(String bagName);

    void nextOrder();
    void previousOrder();

    void previousProduct();
    void nextProduct();
    void buyProduct();
    void orderProduct(String name);
    void orderProduct(Product product, Variant variant);

    void reset()
    {
        orders = {};
        orderIndex = 0;
        ordersLoaded = false;

        products = {};
        productIndex = 0;
        productsLoaded = false;
    };
};

#endif
